IS7V4N/ESP32_E-Reader/Software/crosspoint-reader/src/MappedInputManager.cpp

#include "MappedInputManager.h"

#include "CrossPointSettings.h"

bool MappedInputManager::mapButton(const Button button, bool (HalGPIO::*fn)(uint8_t) const) const {
  switch (button) {
    case Button::Back:
      return (gpio.*fn)(SETTINGS.frontButtonBack);
    case Button::Confirm:
      return (gpio.*fn)(SETTINGS.frontButtonConfirm);
    case Button::Left:
      return (gpio.*fn)(SETTINGS.frontButtonLeft);
    case Button::Right:
      return (gpio.*fn)(SETTINGS.frontButtonRight);
    case Button::Power:
      return (gpio.*fn)(HalGPIO::BTN_POWER);
  }

  return false;
}

bool MappedInputManager::wasPressed(const Button button) const { return mapButton(button, &HalGPIO::wasPressed); }

bool MappedInputManager::wasReleased(const Button button) const { return mapButton(button, &HalGPIO::wasReleased); }

bool MappedInputManager::isPressed(const Button button) const { return mapButton(button, &HalGPIO::isPressed); }

bool MappedInputManager::wasAnyPressed() const { return gpio.wasAnyPressed(); }

bool MappedInputManager::wasAnyReleased() const { return gpio.wasAnyReleased(); }

unsigned long MappedInputManager::getHeldTime() const { return gpio.getHeldTime(); }

MappedInputManager::Labels MappedInputManager::mapLabels(const char* back, const char* confirm, const char* previous,
                                                         const char* next) const {
  // Build the label order based on the configured hardware mapping.
  auto labelForHardware = [&](uint8_t hw) -> const char* {
    // Compare against configured logical roles and return the matching label.
    if (hw == SETTINGS.frontButtonBack) {
      return back;
    }
    if (hw == SETTINGS.frontButtonConfirm) {
      return confirm;
    }
    if (hw == SETTINGS.frontButtonLeft) {
      return previous;
    }
    if (hw == SETTINGS.frontButtonRight) {
      return next;
    }
    return "";
  };

  // Physical left-to-right button order on XteinkX4: LEFT, BACK, CONFIRM, RIGHT
  return {labelForHardware(HalGPIO::BTN_LEFT), labelForHardware(HalGPIO::BTN_BACK),
          labelForHardware(HalGPIO::BTN_CONFIRM), labelForHardware(HalGPIO::BTN_RIGHT)};
}

int MappedInputManager::getPressedFrontButton() const {
  // Scan the raw front buttons in hardware order.
  // This bypasses remapping so the remap activity can capture physical presses.
  if (gpio.wasPressed(HalGPIO::BTN_BACK)) {
    return HalGPIO::BTN_BACK;
  }
  if (gpio.wasPressed(HalGPIO::BTN_CONFIRM)) {
    return HalGPIO::BTN_CONFIRM;
  }
  if (gpio.wasPressed(HalGPIO::BTN_LEFT)) {
    return HalGPIO::BTN_LEFT;
  }
  if (gpio.wasPressed(HalGPIO::BTN_RIGHT)) {
    return HalGPIO::BTN_RIGHT;
  }
  return -1;
}
