IS7V4N/ESP32_E-Reader/Software/crosspoint-reader/src/activities/reader/ReaderUtils.h

#pragma once

#include <CrossPointSettings.h>
#include <GfxRenderer.h>
#include <Logging.h>

#include "MappedInputManager.h"

namespace ReaderUtils {

constexpr unsigned long GO_HOME_MS = 600;
constexpr unsigned long DICTIONARY_LONG_PRESS_MS = 500;

inline void applyOrientation(GfxRenderer& renderer, const uint8_t orientation) {
  switch (orientation) {
    case CrossPointSettings::ORIENTATION::PORTRAIT:
      renderer.setOrientation(GfxRenderer::Orientation::Portrait);
      break;
    case CrossPointSettings::ORIENTATION::LANDSCAPE_CW:
      renderer.setOrientation(GfxRenderer::Orientation::LandscapeClockwise);
      break;
    case CrossPointSettings::ORIENTATION::INVERTED:
      renderer.setOrientation(GfxRenderer::Orientation::PortraitInverted);
      break;
    case CrossPointSettings::ORIENTATION::LANDSCAPE_CCW:
      renderer.setOrientation(GfxRenderer::Orientation::LandscapeCounterClockwise);
      break;
    default:
      break;
  }
}

struct PageTurnResult {
  bool prev;
  bool next;
};

inline PageTurnResult detectPageTurn(const MappedInputManager& input) {
  const bool usePress = !SETTINGS.longPressChapterSkip;
  const bool prev = usePress ? input.wasPressed(MappedInputManager::Button::Left)
                             : input.wasReleased(MappedInputManager::Button::Left);
  const bool powerTurn = SETTINGS.shortPwrBtn == CrossPointSettings::SHORT_PWRBTN::PAGE_TURN &&
                         input.wasReleased(MappedInputManager::Button::Power);
  const bool next = usePress ? (powerTurn || input.wasPressed(MappedInputManager::Button::Right))
                             : (powerTurn || input.wasReleased(MappedInputManager::Button::Right));
  return {prev, next};
}

inline void displayWithRefreshCycle(const GfxRenderer& renderer, int& pagesUntilFullRefresh) {
  if (pagesUntilFullRefresh <= 1) {
    renderer.displayBuffer(HalDisplay::HALF_REFRESH);
    pagesUntilFullRefresh = SETTINGS.getRefreshFrequency();
  } else {
    renderer.displayBuffer();
    pagesUntilFullRefresh--;
  }
}

// Grayscale anti-aliasing pass. Renders content twice (LSB + MSB) to build
// the grayscale buffer. Only the content callback is re-rendered — status bars
// and other overlays should be drawn before calling this.
// Kept as a template to avoid std::function overhead; instantiated once per reader type.
template <typename RenderFn>
void renderAntiAliased(GfxRenderer& renderer, RenderFn&& renderFn) {
  if (!renderer.storeBwBuffer()) {
    LOG_ERR("READER", "Failed to store BW buffer for anti-aliasing");
    return;
  }

  renderer.clearScreen(0x00);
  renderer.setRenderMode(GfxRenderer::GRAYSCALE_LSB);
  renderFn();
  renderer.copyGrayscaleLsbBuffers();

  renderer.clearScreen(0x00);
  renderer.setRenderMode(GfxRenderer::GRAYSCALE_MSB);
  renderFn();
  renderer.copyGrayscaleMsbBuffers();

  renderer.displayGrayBuffer();
  renderer.setRenderMode(GfxRenderer::BW);

  renderer.restoreBwBuffer();
}

}  // namespace ReaderUtils
